NeuraCoreTech/NeuraCore-PCB/V01/zynqPCB/images/blockdiagram.PNG

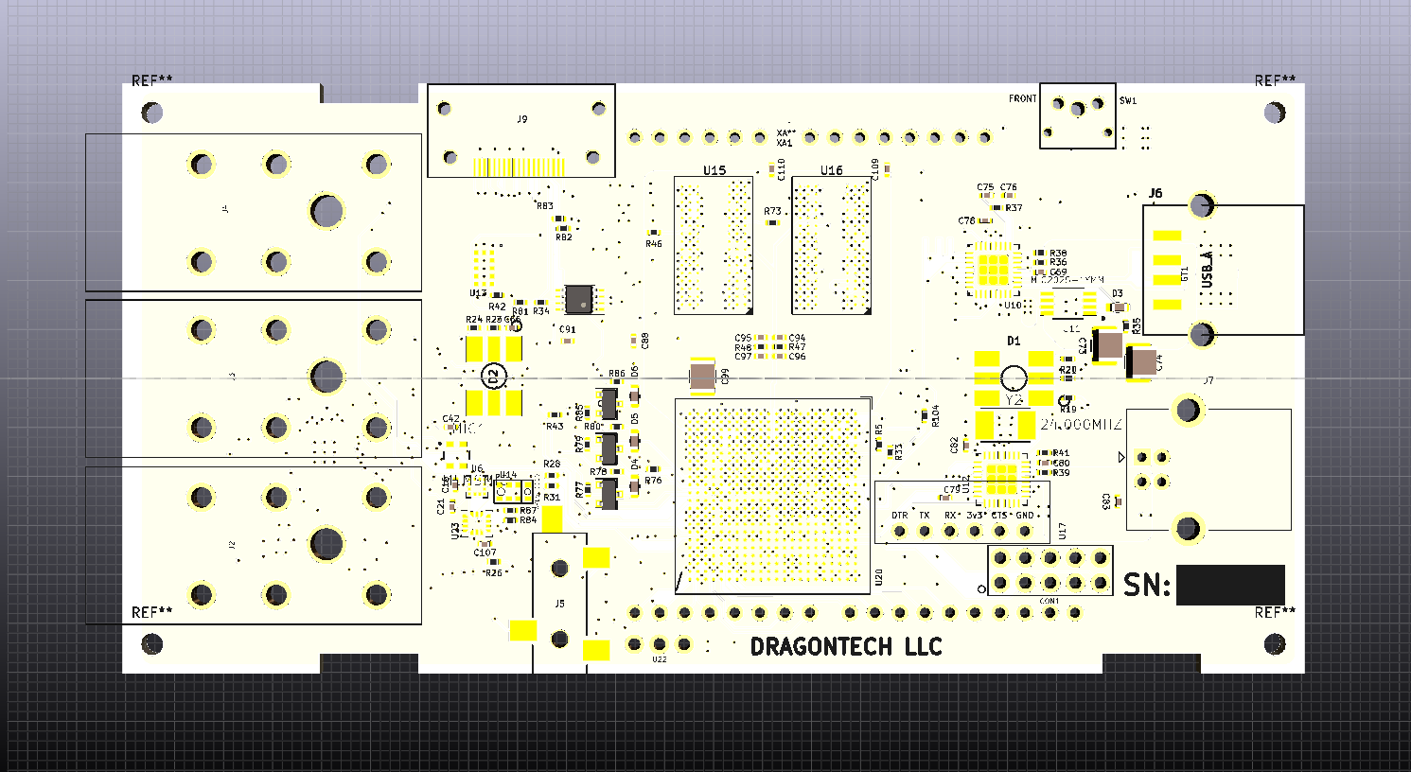
V01/zynqPCB/images/blockdiagram.PNG
